Protocentral/HeartyBadge/firmware/hrv_badge_ble/main/max30003.h

#ifndef MAX30003_H_
#define MAX30003_H_

#define WREG 0x00
#define RREG 0x01

#define   STATUS          0x01
#define   EN_INT          0x02
#define   EN_INT2         0x03
#define   MNGR_INT        0x04
#define   MNGR_DYN        0x05
#define   SW_RST          0x08
#define   SYNCH           0x09
#define   FIFO_RST        0x0A
#define   INFO            0x0F
#define   CNFG_GEN        0x10
#define   CNFG_CAL        0x12
#define   CNFG_EMUX       0x14
#define   CNFG_ECG        0x15
#define   CNFG_RTOR1      0x1D
#define   CNFG_RTOR2      0x1E
#define   ECG_FIFO_BURST  0x20
#define   ECG_FIFO        0x21
#define   RTOR            0x25
#define   NO_OP           0x7F

#define PIN_NUM_FCLK      13
#define MAX30003_INT_PIN  27// for kalam board02
#define MAX 60

#define PIN_I2C_SDA  21
#define PIN_I2C_SCL  22

#define PIN_SPI_CS   4
#define PIN_SPI_MOSI 23
#define PIN_SPI_MISO 19
#define PIN_SPI_SCK  18


volatile unsigned int HR ,RR ;

 xQueueHandle rgbLedSem;
QueueHandle_t xQueue_tcp;

void kalam_start_max30003();
void max30003_start_timer(void);
void MAX30003_ReadID(void);
void max30003_initchip(int pin_miso, int pin_mosi, int pin_sck, int pin_cs );
uint8_t* max30003_read_send_data(void );
//void arrhythmia(unsigned int array[MAX]);
float pnn_ff(unsigned int queue_array[MAX]);
float mean(unsigned int queue_array[MAX]);
float sdnn_ff(unsigned int queue_array[]);
int max(unsigned int array[]);
int min(unsigned int array[]);
void kalam32_uart_init(void);


//float trindex(unsigned int array[]);
//void print(void *pvParameters);


#endif
